Jay-esp/router_lift/IMG_4641.PNG

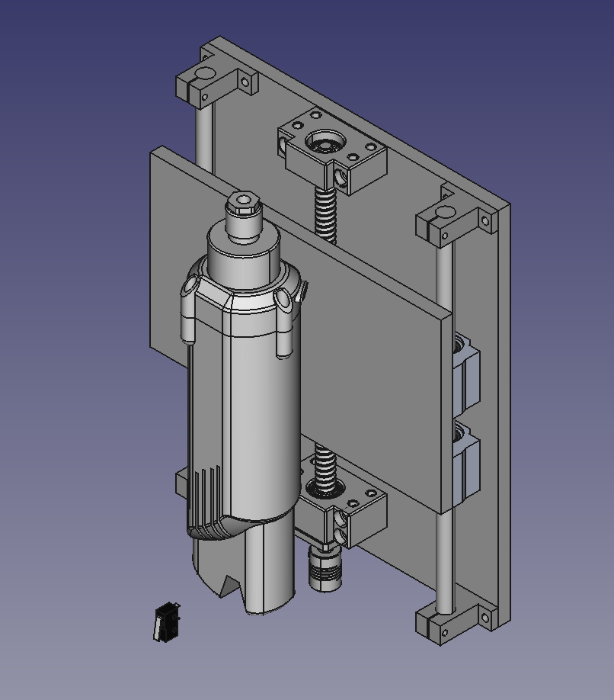
IMG_4641.PNG
