Jay-esp/router_lift/IMG_4643.PNG

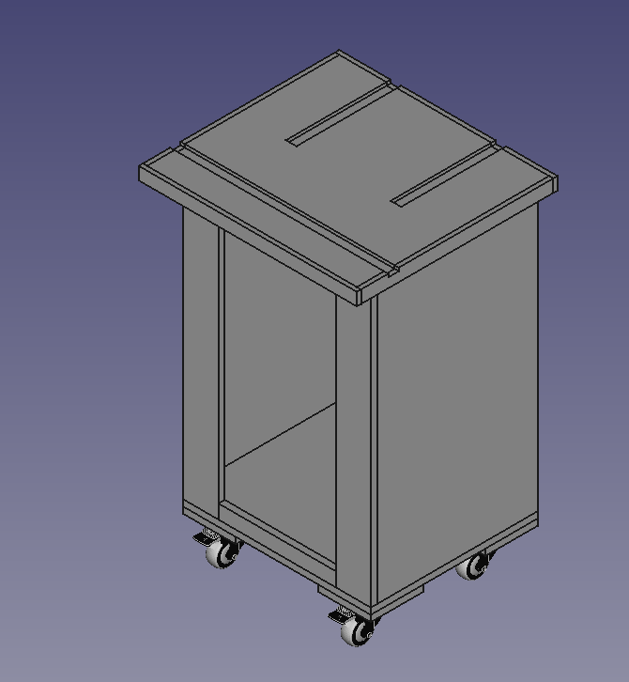
IMG_4643.PNG
