Jay-esp/router_lift/src/router_table_9/dseg_175.c

/*******************************************************************************
 * Size: 175 px
 * Bpp: 1
 * Opts: --bpp 1 --size 175 --no-compress --font Seven Segment.ttf --symbols  01234567890.,-+ --format lvgl -o dseg_175.c
 ******************************************************************************/


#include "lvgl.h"


#ifndef DSEG_175
#define DSEG_175 1
#endif

#if DSEG_175

/*-----------------
 *    BITMAPS
 *----------------*/

/*Store the image of the glyphs*/
static LV_ATTRIBUTE_LARGE_CONST const uint8_t glyph_bitmap[] = {
    /* U+0020 " " */
    0x0,

    /* U+002B "+" */
    0x0, 0x0, 0x0, 0x0, 0x0, 0x1, 0x0, 0x0,
    0x0, 0x0, 0x0, 0x0, 0x0, 0x0, 0x0, 0x0,
    0x0, 0x7, 0x0, 0x0, 0x0, 0x0, 0x0, 0x0,
    0x0, 0x0, 0x0, 0x0, 0x0, 0x1f, 0x0, 0x0,
    0x0, 0x0, 0x0, 0x0, 0x0, 0x0, 0x0, 0x0,
    0x0, 0x7f, 0x0, 0x0, 0x0, 0x0, 0x0, 0x0,
    0x0, 0x0, 0x0, 0x0, 0x1, 0xff, 0x0, 0x0,
    0x0, 0x0, 0x0, 0x0, 0x0, 0x0, 0x0, 0x0,
    0x7, 0xff, 0x0, 0x0, 0x0, 0x0, 0x0, 0x0,
    0x0, 0x0, 0x0, 0x0, 0xf, 0xfe, 0x0, 0x0,
    0x0, 0x0, 0x0, 0x0, 0x0, 0x0, 0x0, 0x0,
    0x1f, 0xfc, 0x0, 0x0, 0x0, 0x0, 0x0, 0x0,
    0x0, 0x0, 0x0, 0x0, 0x3f, 0xf8, 0x0, 0x0,
    0x0, 0x0, 0x0, 0x0, 0x0, 0x0, 0x0, 0x0,
    0x7f, 0xf0, 0x0, 0x0, 0x0, 0x0, 0x0, 0x0,
    0x0, 0x0, 0x0, 0x0, 0xff, 0xe0, 0x0, 0x0,
    0x0, 0x0, 0x0, 0x0, 0x0, 0x0, 0x0, 0x1,
    0xff, 0xc0, 0x0, 0x0, 0x0, 0x0, 0x0, 0x0,
    0x0, 0x0, 0x0, 0x3, 0xff, 0x80, 0x0, 0x0,
    0x0, 0x0, 0x0, 0x0, 0x0, 0x0, 0x0, 0x7,
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
    0x0, 0x0, 0x0, 0x1f, 0xff, 0xff, 0x80, 0x0,
    0x0, 0x0, 0x0, 0x3, 0xff, 0xff, 0xf0, 0x0,
    0x0, 0x0, 0x0, 0x0, 0x7f, 0xff, 0xfe, 0x0,
    0x0, 0x0, 0x0, 0x0, 0xf, 0xff, 0xff, 0xc0,
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
};


/*---------------------
 *  GLYPH DESCRIPTION
 *--------------------*/

static const lv_font_fmt_txt_glyph_dsc_t glyph_dsc[] = {
    {.bitmap_index = 0, .adv_w = 0, .box_w = 0, .box_h = 0, .ofs_x = 0, .ofs_y = 0} /* id = 0 reserved */,
    {.bitmap_index = 0, .adv_w = 839, .box_w = 1, .box_h = 1, .ofs_x = 0, .ofs_y = 0},
    {.bitmap_index = 1, .adv_w = 1850, .box_w = 95, .box_h = 95, .ofs_x = 10, .ofs_y = 9},
    {.bitmap_index = 1130, .adv_w = 647, .box_w = 20, .box_h = 20, .ofs_x = 11, .ofs_y = 0},
    {.bitmap_index = 1180, .adv_w = 1136, .box_w = 50, .box_h = 11, .ofs_x = 11, .ofs_y = 56},
    {.bitmap_index = 1249, .adv_w = 514, .box_w = 11, .box_h = 17, .ofs_x = 11, .ofs_y = 0},
    {.bitmap_index = 1273, .adv_w = 1405, .box_w = 67, .box_h = 123, .ofs_x = 11, .ofs_y = 0},
    {.bitmap_index = 2304, .adv_w = 514, .box_w = 11, .box_h = 123, .ofs_x = 11, .ofs_y = 0},
    {.bitmap_index = 2474, .adv_w = 1405, .box_w = 67, .box_h = 123, .ofs_x = 11, .ofs_y = 0},
    {.bitmap_index = 3505, .adv_w = 1273, .box_w = 58, .box_h = 123, .ofs_x = 11, .ofs_y = 0},
    {.bitmap_index = 4397, .adv_w = 1405, .box_w = 67, .box_h = 123, .ofs_x = 11, .ofs_y = 0},
    {.bitmap_index = 5428, .adv_w = 1405, .box_w = 67, .box_h = 123, .ofs_x = 11, .ofs_y = 0},
    {.bitmap_index = 6459, .adv_w = 1405, .box_w = 67, .box_h = 123, .ofs_x = 11, .ofs_y = 0},
    {.bitmap_index = 7490, .adv_w = 1273, .box_w = 58, .box_h = 123, .ofs_x = 11, .ofs_y = 0},
    {.bitmap_index = 8382, .adv_w = 1405, .box_w = 67, .box_h = 123, .ofs_x = 11, .ofs_y = 0},
    {.bitmap_index = 9413, .adv_w = 1405, .box_w = 67, .box_h = 123, .ofs_x = 11, .ofs_y = 0}
};

/*---------------------
 *  CHARACTER MAPPING
 *--------------------*/

static const uint8_t glyph_id_ofs_list_0[] = {
    0, 0, 0, 0, 0, 0, 0, 0,
    0, 0, 0, 1, 2, 3, 4, 0,
    5, 6, 7, 8, 9, 10, 11, 12,
    13, 14
};

/*Collect the unicode lists and glyph_id offsets*/
static const lv_font_fmt_txt_cmap_t cmaps[] =
{
    {
        .range_start = 32, .range_length = 26, .glyph_id_start = 1,
        .unicode_list = NULL, .glyph_id_ofs_list = glyph_id_ofs_list_0, .list_length = 26, .type = LV_FONT_FMT_TXT_CMAP_FORMAT0_FULL
    }
};



/*--------------------
 *  ALL CUSTOM DATA
 *--------------------*/

#if LVGL_VERSION_MAJOR == 8
/*Store all the custom data of the font*/
static  lv_font_fmt_txt_glyph_cache_t cache;
#endif

#if LVGL_VERSION_MAJOR >= 8
static const lv_font_fmt_txt_dsc_t font_dsc = {
#else
static lv_font_fmt_txt_dsc_t font_dsc = {
#endif
    .glyph_bitmap = glyph_bitmap,
    .glyph_dsc = glyph_dsc,
    .cmaps = cmaps,
    .kern_dsc = NULL,
    .kern_scale = 0,
    .cmap_num = 1,
    .bpp = 1,
    .kern_classes = 0,
    .bitmap_format = 0,
#if LVGL_VERSION_MAJOR == 8
    .cache = &cache
#endif
};



/*-----------------
 *  PUBLIC FONT
 *----------------*/

/*Initialize a public general font descriptor*/
#if LVGL_VERSION_MAJOR >= 8
const lv_font_t dseg_175 = {
#else
lv_font_t dseg_175 = {
#endif
    .get_glyph_dsc = lv_font_get_glyph_dsc_fmt_txt,    /*Function pointer to get glyph's data*/
    .get_glyph_bitmap = lv_font_get_bitmap_fmt_txt,    /*Function pointer to get glyph's bitmap*/
    .line_height = 123,          /*The maximum line height required by the font*/
    .base_line = 0,             /*Baseline measured from the bottom of the line*/
#if !(LVGL_VERSION_MAJOR == 6 && LVGL_VERSION_MINOR == 0)
    .subpx = LV_FONT_SUBPX_NONE,
#endif
#if LV_VERSION_CHECK(7, 4, 0) || LVGL_VERSION_MAJOR >= 8
    .underline_position = -57,
    .underline_thickness = 9,
#endif
    .dsc = &font_dsc,          /*The custom font data. Will be accessed by `get_glyph_bitmap/dsc` */
#if LV_VERSION_CHECK(8, 2, 0) || LVGL_VERSION_MAJOR >= 9
    .fallback = NULL,
#endif
    .user_data = NULL,
};



#endif /*#if DSEG_175*/
