Jay-esp/router_lift/src/router_table_9/dseg_60.c

/*******************************************************************************
 * Size: 60 px
 * Bpp: 1
 * Opts: --bpp 1 --size 60 --no-compress --font DSEG7ClassicMini-Regular.ttf --symbols 0123456789.,-  --format lvgl -o dseg_60.c
 ******************************************************************************/


#include "lvgl.h"

#ifndef DSEG_60
#define DSEG_60 1
#endif

#if DSEG_60

/*-----------------
 *    BITMAPS
 *----------------*/

/*Store the image of the glyphs*/
static LV_ATTRIBUTE_LARGE_CONST const uint8_t glyph_bitmap[] = {
    /* U+0020 " " */
    0x0,

    /* U+002D "-" */
    0x1f, 0xff, 0xff, 0xc1, 0xff, 0xff, 0xff, 0x3f,
    0xff, 0xff, 0xfe, 0x7f, 0xff, 0xff, 0xc1, 0xff,
    0xff, 0xfc, 0x0,

    /* U+002E "." */
    0x38, 0xfb, 0xff, 0xff, 0xef, 0x8e, 0x0,

    /* U+0030 "0" */
    0x3, 0xff, 0xff, 0xfe, 0x0, 0x3f, 0xff, 0xff,
    0xf8, 0x0, 0xff, 0xff, 0xff, 0x80, 0x3, 0xff,
    0xff, 0xf8, 0x6, 0xf, 0xff, 0xff, 0x83, 0x78,
    0x0, 0x0, 0x0, 0x3f, 0xe0, 0x0, 0x0, 0x3,
    0xff, 0x80, 0x0, 0x0, 0x3f, 0xfc, 0x0, 0x0,
    0x1, 0xff, 0xe0, 0x0, 0x0, 0xf, 0xff, 0x0,
    0x0, 0x0, 0x7f, 0xf8, 0x0, 0x0, 0x3, 0xff,
    0xc0, 0x0, 0x0, 0x1f, 0xfe, 0x0, 0x0, 0x0,
    0xff, 0xf0, 0x0, 0x0, 0x7, 0xff, 0x80, 0x0,
    0x0, 0x3f, 0xfc, 0x0, 0x0, 0x1, 0xff, 0xe0,
    0x0, 0x0, 0xf, 0xff, 0x0, 0x0, 0x0, 0x7f,
    0xf8, 0x0, 0x0, 0x3, 0xff, 0xc0, 0x0, 0x0,
    0x1f, 0xfe, 0x0, 0x0, 0x0, 0xff, 0xf0, 0x0,
    0x0, 0x7, 0xff, 0x80, 0x0, 0x0, 0x3f, 0xf8,
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
    0x0, 0x7c, 0x0, 0x0, 0x0, 0x1, 0xe0, 0x1f,
    0xff, 0xff, 0x6, 0x1, 0xff, 0xff, 0xfc, 0x0,
    0x1f, 0xff, 0xff, 0xf0, 0x1, 0xff, 0xff, 0xff,
    0xc0, 0x7, 0xff, 0xff, 0xfc, 0x0
};


/*---------------------
 *  GLYPH DESCRIPTION
 *--------------------*/

static const lv_font_fmt_txt_glyph_dsc_t glyph_dsc[] = {
    {.bitmap_index = 0, .adv_w = 0, .box_w = 0, .box_h = 0, .ofs_x = 0, .ofs_y = 0} /* id = 0 reserved */,
    {.bitmap_index = 0, .adv_w = 192, .box_w = 1, .box_h = 1, .ofs_x = 0, .ofs_y = 0},
    {.bitmap_index = 1, .adv_w = 783, .box_w = 29, .box_h = 5, .ofs_x = 10, .ofs_y = 27},
    {.bitmap_index = 20, .adv_w = 0, .box_w = 7, .box_h = 7, .ofs_x = -4, .ofs_y = 0},
    {.bitmap_index = 27, .adv_w = 783, .box_w = 37, .box_h = 60, .ofs_x = 6, .ofs_y = 0},
    {.bitmap_index = 305, .adv_w = 783, .box_w = 6, .box_h = 52, .ofs_x = 37, .ofs_y = 4},
    {.bitmap_index = 344, .adv_w = 783, .box_w = 37, .box_h = 60, .ofs_x = 6, .ofs_y = 0},
    {.bitmap_index = 622, .adv_w = 783, .box_w = 33, .box_h = 60, .ofs_x = 10, .ofs_y = 0},
    {.bitmap_index = 870, .adv_w = 783, .box_w = 37, .box_h = 51, .ofs_x = 6, .ofs_y = 4},
    {.bitmap_index = 1106, .adv_w = 783, .box_w = 37, .box_h = 60, .ofs_x = 6, .ofs_y = 0},
    {.bitmap_index = 1384, .adv_w = 783, .box_w = 37, .box_h = 60, .ofs_x = 6, .ofs_y = 0},
    {.bitmap_index = 1662, .adv_w = 783, .box_w = 37, .box_h = 55, .ofs_x = 6, .ofs_y = 5},
    {.bitmap_index = 1917, .adv_w = 783, .box_w = 37, .box_h = 60, .ofs_x = 6, .ofs_y = 0},
    {.bitmap_index = 2195, .adv_w = 783, .box_w = 37, .box_h = 60, .ofs_x = 6, .ofs_y = 0}
};

/*---------------------
 *  CHARACTER MAPPING
 *--------------------*/

static const uint16_t unicode_list_0[] = {
    0x0, 0xd, 0xe
};

/*Collect the unicode lists and glyph_id offsets*/
static const lv_font_fmt_txt_cmap_t cmaps[] =
{
    {
        .range_start = 32, .range_length = 15, .glyph_id_start = 1,
        .unicode_list = unicode_list_0, .glyph_id_ofs_list = NULL, .list_length = 3, .type = LV_FONT_FMT_TXT_CMAP_SPARSE_TINY
    },
    {
        .range_start = 48, .range_length = 10, .glyph_id_start = 4,
        .unicode_list = NULL, .glyph_id_ofs_list = NULL, .list_length = 0, .type = LV_FONT_FMT_TXT_CMAP_FORMAT0_TINY
    }
};



/*--------------------
 *  ALL CUSTOM DATA
 *--------------------*/

#if LVGL_VERSION_MAJOR == 8
/*Store all the custom data of the font*/
static  lv_font_fmt_txt_glyph_cache_t cache;
#endif

#if LVGL_VERSION_MAJOR >= 8
static const lv_font_fmt_txt_dsc_t font_dsc = {
#else
static lv_font_fmt_txt_dsc_t font_dsc = {
#endif
    .glyph_bitmap = glyph_bitmap,
    .glyph_dsc = glyph_dsc,
    .cmaps = cmaps,
    .kern_dsc = NULL,
    .kern_scale = 0,
    .cmap_num = 2,
    .bpp = 1,
    .kern_classes = 0,
    .bitmap_format = 0,
#if LVGL_VERSION_MAJOR == 8
    .cache = &cache
#endif
};



/*-----------------
 *  PUBLIC FONT
 *----------------*/

/*Initialize a public general font descriptor*/
#if LVGL_VERSION_MAJOR >= 8
const lv_font_t dseg_60 = {
#else
lv_font_t dseg_60 = {
#endif
    .get_glyph_dsc = lv_font_get_glyph_dsc_fmt_txt,    /*Function pointer to get glyph's data*/
    .get_glyph_bitmap = lv_font_get_bitmap_fmt_txt,    /*Function pointer to get glyph's bitmap*/
    .line_height = 60,          /*The maximum line height required by the font*/
    .base_line = 0,             /*Baseline measured from the bottom of the line*/
#if !(LVGL_VERSION_MAJOR == 6 && LVGL_VERSION_MINOR == 0)
    .subpx = LV_FONT_SUBPX_NONE,
#endif
#if LV_VERSION_CHECK(7, 4, 0) || LVGL_VERSION_MAJOR >= 8
    .underline_position = -7,
    .underline_thickness = 3,
#endif
    .dsc = &font_dsc,          /*The custom font data. Will be accessed by `get_glyph_bitmap/dsc` */
#if LV_VERSION_CHECK(8, 2, 0) || LVGL_VERSION_MAJOR >= 9
    .fallback = NULL,
#endif
    .user_data = NULL,
};



#endif /*#if DSEG_60*/
